g4eml/RP2040_OOK48_LCD/Arduino/RP2040_OOK48_LCD/globals.h

#include "morse_rx.h"
//Global variables

//EEPROM Structure. This structure is written to the EEPROM. All members are therefore non-volatile. 

struct eepromstruct
{
  uint8_t calMagic;               //calibration magic value to indicate validity
  uint16_t calData[5];            //screen calibration data
  uint8_t baudMagic;              //baud rate magic value to indicate validity
  uint16_t gpsBaud;               //GPS baud rate
  uint8_t messageMagic;          //message magic value to indicate validity
  char TxMessage[10][32];         //message storage
  uint8_t locatorLength;          //Default QTH Locator
  uint8_t decodeMode;             //allow multiple decode modes
  uint16_t txAdvance;             //Tx timing advance in ms
  uint16_t rxRetard;              //Rx Timing retard in ms
  float batcal;                   //battery voltage calibration factor
  uint8_t app;                    //currently selected application OOK48 JT4G or PI4
  uint8_t  morseWpm;              //Morse WPM

};

struct eepromstruct settings;

enum decodemodes {NORMALMODE,ALTMODE};

enum core1Message {GENPLOT,DRAWSPECTRUM,DRAWWATERFALL,REDLINE,CYANLINE,MESSAGE,TMESSAGE,JTMESSAGE,PIMESSAGE,MORSEMESSAGE,MORSELOCKED,MORSELOST};         //messages for control of Core 1 from Core 2


uint16_t dma_chan;                        //DMA Channel Number
bool dmaReady;                        //Flag to indicate a DMA buffer is ready to be processed.
uint8_t bufIndex = 0;                 //Index to the current DMA buffer. Alternates 0/1.

enum apps {OOK48,MORSE,BEACONJT4,BEACONPI4};

uint8_t mode;
enum modes {RX,TX};

uint8_t beaconMode;
enum bmodes {JT4,PI4};

uint32_t sampleRate;                  //samples per second.
uint16_t rxToneBin;                      //tone in bins. 
uint16_t toneTolerance;             //Tone tolerance in bins. 
uint16_t cacheSize;                 // tone decode samples.
float hzPerBin;
uint16_t activeBins;
int overlap = 1;
int numberOfTones =1;
int numberOfBins;
int startBin;

//Beacon mode variables
uint16_t toneSpacing;                //tone spacing in number of bins.
uint16_t tone0;                      //tone zero in bins.
uint16_t symbolCount;               //number of symbols message.
uint16_t bitCount;                  //number of bits in Message
uint8_t BeaconToneCache[JT4CACHESIZE];         // Array for tone cache (JT4 is larger than PI4 so we will use that for both.)
char JTmessage[14];                     //decoded JT4 Message
char PImessage[9];                      //decoded PI4 Message

float sigNoise;
float snBins;
float threshold;
float toneCache[JT4NUMBEROFBINS][CACHESIZE *2];          // Array large enough for the biggest tone magnitude cache
uint16_t cachePoint;                  // Pointer to next cache entry. 
bool halfRate = false;

char decoded;                         //decoded  Message character

char gpsBuffer[256];                     //GPS data buffer
int gpsPointer;                          //GPS buffer pointer. 
char gpsCh;
bool GPSDebug = false;
bool gpsActive = false; 
int lastSec = 0;
int gpsSec = -1;                       //GPS clock time  -1 for GPS Invalid
int gpsMin = -1;
int gpsHr = -1;
int gpsDay= -1;
int gpsMonth = -1;
int gpsYear = -1;
uint8_t PPSActive = 0;
long lastTimeUpdate = 0;
long lastmin;                         // Timing variable
float latitude = 0;
float longitude =0;
char qthLocator[12] = "----------";

uint16_t buffer[2][NUMBEROFOVERSAMPLES];     //2 DMA buffers to allow one to be processed while the next is being received.
float sample[NUMBEROFSAMPLES];              //array for the averaged samples 
float sampleI[NUMBEROFSAMPLES];             //imaginary part for FFT
float magnitude[JT4NUMBEROFBINS];            //Array for signal spectrum
uint8_t  audioLevel;    // RX audio level 0-100 (peak-smoothed, for volume guidance)

uint16_t t_x = 0, t_y = 0;            // To store the touch coordinates
uint16_t textrow;                    //current row for text output
uint16_t textcol;                    //current colume position for text output
uint8_t waterRow;                 //Counter for current Waterfall display row. 
bool autolevel = true;

uint16_t textHeight;

bool noTouch = true;

int TxPointer = 0;
uint8_t TxBitPointer = 0;
uint8_t TxBuffer[50];                       //needs to be large enough to allow for Locator Expansion
char visualTxMessage[50];
uint8_t TxMessNo;
uint8_t TxMessLen;
bool Key;
bool TxSent;
char TxCharSent;
bool messageChanging;

bool sdpresent;

// Morse RX
MorseRxDecoder morseDecoder;
float morseWpmEst;    // WPM at lock, for status display
float morseWpmCurrent;  //Current tracking morse WPM
uint32_t dmaTransferCount;  // set by RxInit(), read by dma_init()

uint8_t plotData[SPECWIDTH];        //Array of Plot points for spectrum display. Log scaled and offset to 0 - SPECHEIGHT and used to display new line.  
uint8_t lastplotData[SPECWIDTH];    //Array of Plot points for last Spectrum display. Used to erase previous line.

uint8_t toneLegend[4][2];                  // start and end pixels for tone indicator legend

//Waterfall Display colours. Based on Spectravue values. 
uint16_t waterColours[256] =
{0X0, 0X1, 0X2, 0X3, 0X4, 0X5, 0X6, 0X7, 0X7, 0X8, 0X9, 0XA, 0XB, 0XC, 0XD, 0XE,
 0XE, 0XF, 0X10, 0X11, 0X12, 0X13, 0X14, 0X15, 0X15, 0X16, 0X17, 0X18, 0X19, 0X1A,
 0X1B, 0X1C, 0X3C, 0X5C, 0X7C, 0X9C, 0XBC, 0XDC, 0X11C, 0X13C, 0X15C, 0X17C, 0X19D,
 0X1BD, 0X1FD, 0X21D, 0X23D, 0X25D, 0X27D, 0X29D, 0X2BD, 0X2FD, 0X31D, 0X33E, 0X35E,
 0X37E, 0X39E, 0X3DE, 0X3FE, 0X41E, 0X43E, 0X45E, 0X47E, 0X4BF, 0X4BE, 0X4DE, 0X4FE,
 0X51E, 0X53D, 0X53D, 0X55D, 0X57D, 0X59C, 0X5BC, 0X5BC, 0X5DC, 0X5FB, 0X61B, 0X63B,
 0X65B, 0X65A, 0X67A, 0X69A, 0X6BA, 0X6D9, 0X6D9, 0X6F9, 0X719, 0X738, 0X758, 0X758,
 0X778, 0X797, 0X7B7, 0X7D7, 0X7F7, 0X7F6, 0X7F5, 0X7F4, 0X7F4, 0X7F3, 0X7F2, 0XFF1, 
 0XFF1, 0XFF0, 0XFEF, 0XFEF, 0XFEE, 0X17ED, 0X17EC, 0X17EC, 0X17EB, 0X17EA, 0X17EA, 
 0X17E9, 0X1FE8, 0X1FE7, 0X1FE7, 0X1FE6, 0X1FE5, 0X1FE5, 0X27E4, 0X27E3, 0X27E2, 
 0X27E2, 0X27E1, 0X27E0, 0X2FE0, 0X2FE0, 0X37E0, 0X3FE0, 0X47E0, 0X4FE0, 0X4FE0, 
 0X57E0, 0X5FE0, 0X67E0, 0X6FE0, 0X6FE0, 0X77E0, 0X7FE0, 0X87E0, 0X8FE0, 0X97E0, 
 0X97E0, 0X9FE0, 0XA7E0, 0XAFE0, 0XB7E0, 0XB7E0, 0XBFE0, 0XC7E0, 0XCFE0, 0XD7E0, 
 0XD7E0, 0XDFE0, 0XE7E0, 0XEFE0, 0XF7E0, 0XFFE0, 0XFFC0, 0XFFA0, 0XFF80, 0XFF60, 
 0XFF40, 0XFF20, 0XFF00, 0XFEE0, 0XFEC0, 0XFEA0, 0XFEA0, 0XFE80, 0XFE60, 0XFE40, 
 0XFE20, 0XFE00, 0XFDE0, 0XFDC0, 0XFDA0, 0XFD80, 0XFD60, 0XFD60, 0XFD40, 0XFD20, 
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
35,108,71,144,2,75,39,112,21,94,57,130,12,85,48,121,30,103,66,139,7,80,43,116,25,98,61,134,16,89,
52,125,34,107,70,143,4,77,41,114,23,96,59,132,14,87,50,123,32,105,68,141,9,82,45,118,27,100,63,136,
18,91,54,127,36,109,72,145,1,74,38,111,20,93,56,129,11,84,47,120,29,102,65,138,6,79
}; 
